sercami97/EstacionMeteorologica/Documentacion/img/ardu.jpg

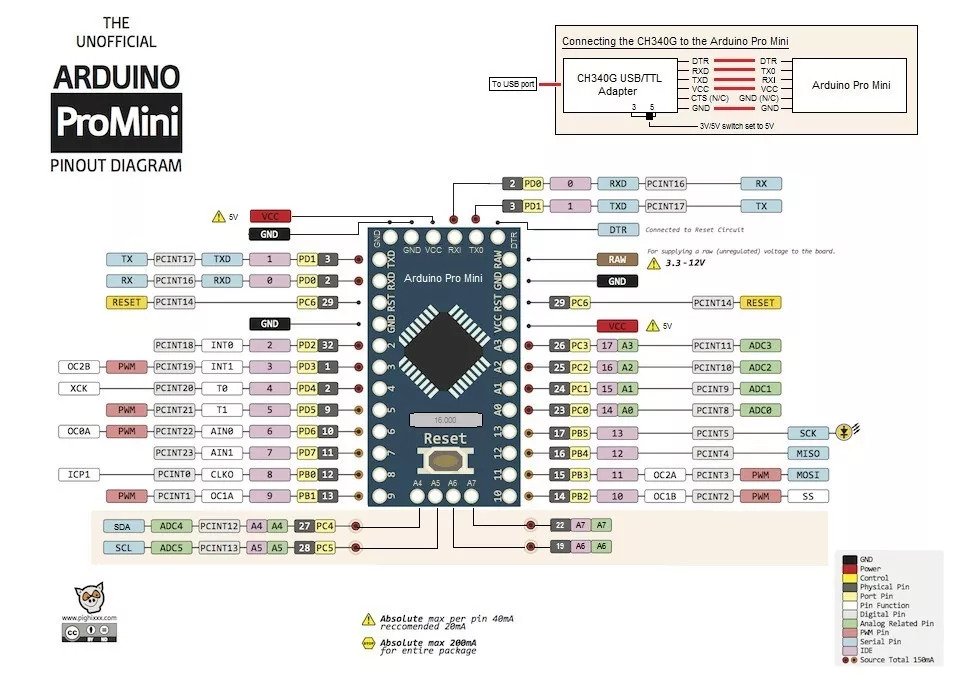
Documentacion/img/ardu.jpg
