sercami97/EstacionMeteorologica/Documentacion/img/dgen.png

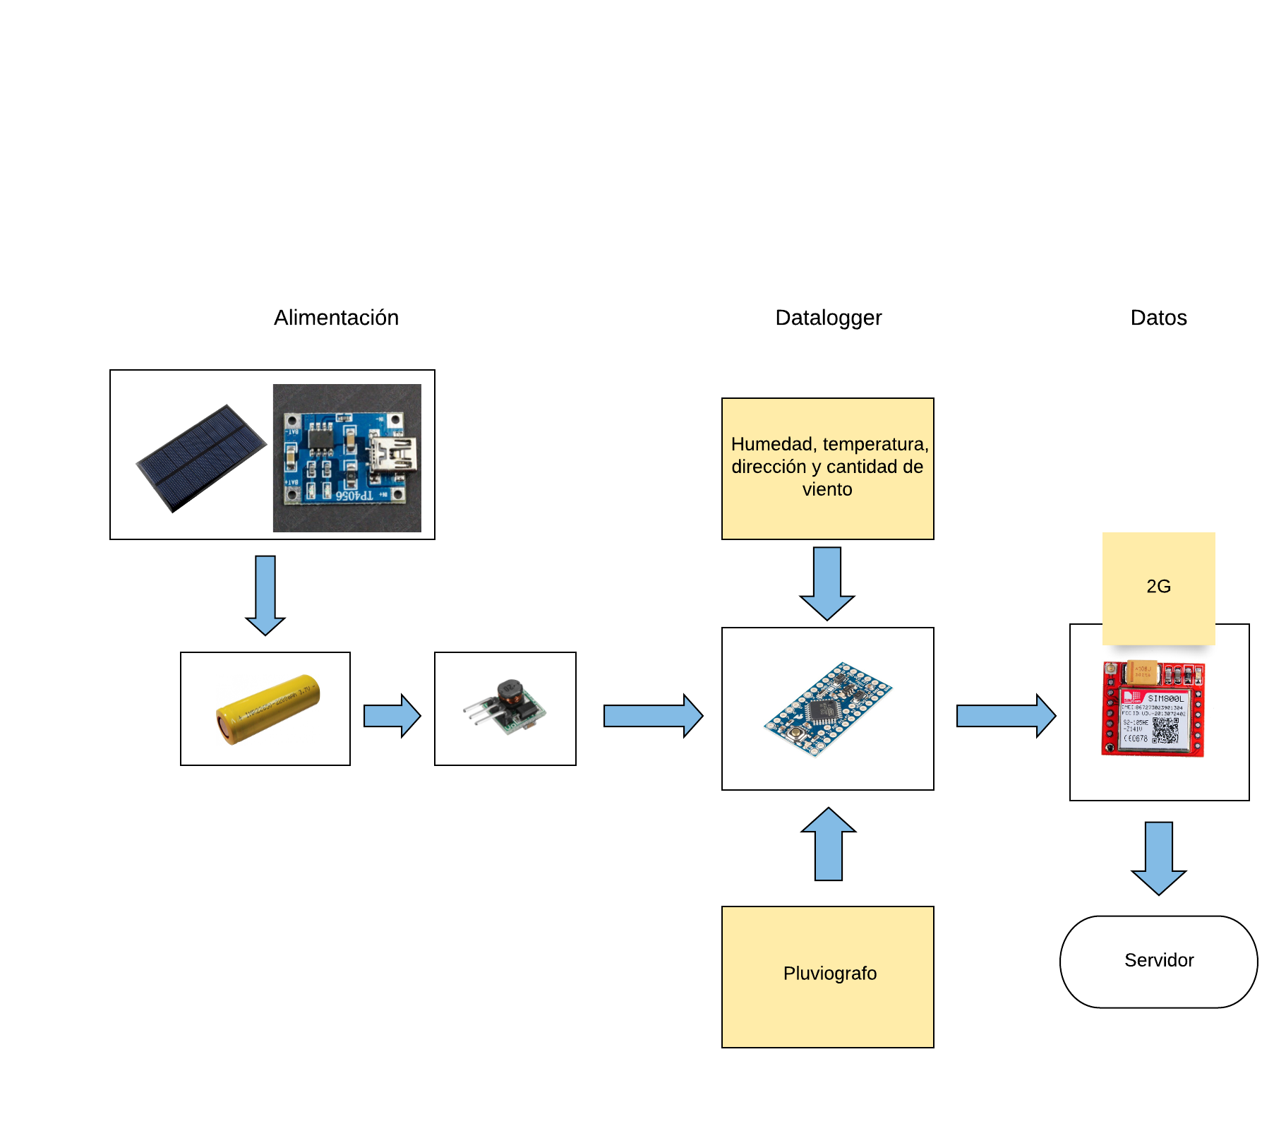
Documentacion/img/dgen.png
