sercami97/EstacionMeteorologica/Documentacion/img/dir_viento.png

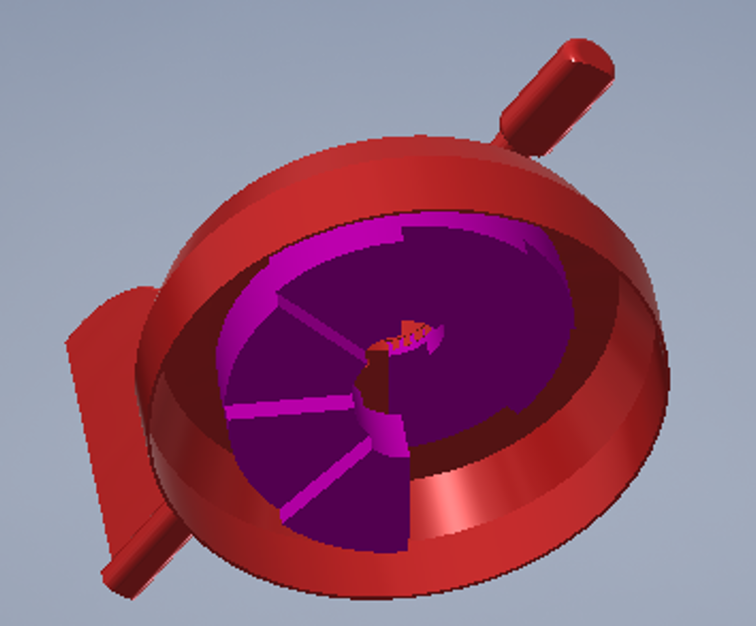
Documentacion/img/dir_viento.png
