sercami97/EstacionMeteorologica/Documentacion/img/dsleep.png

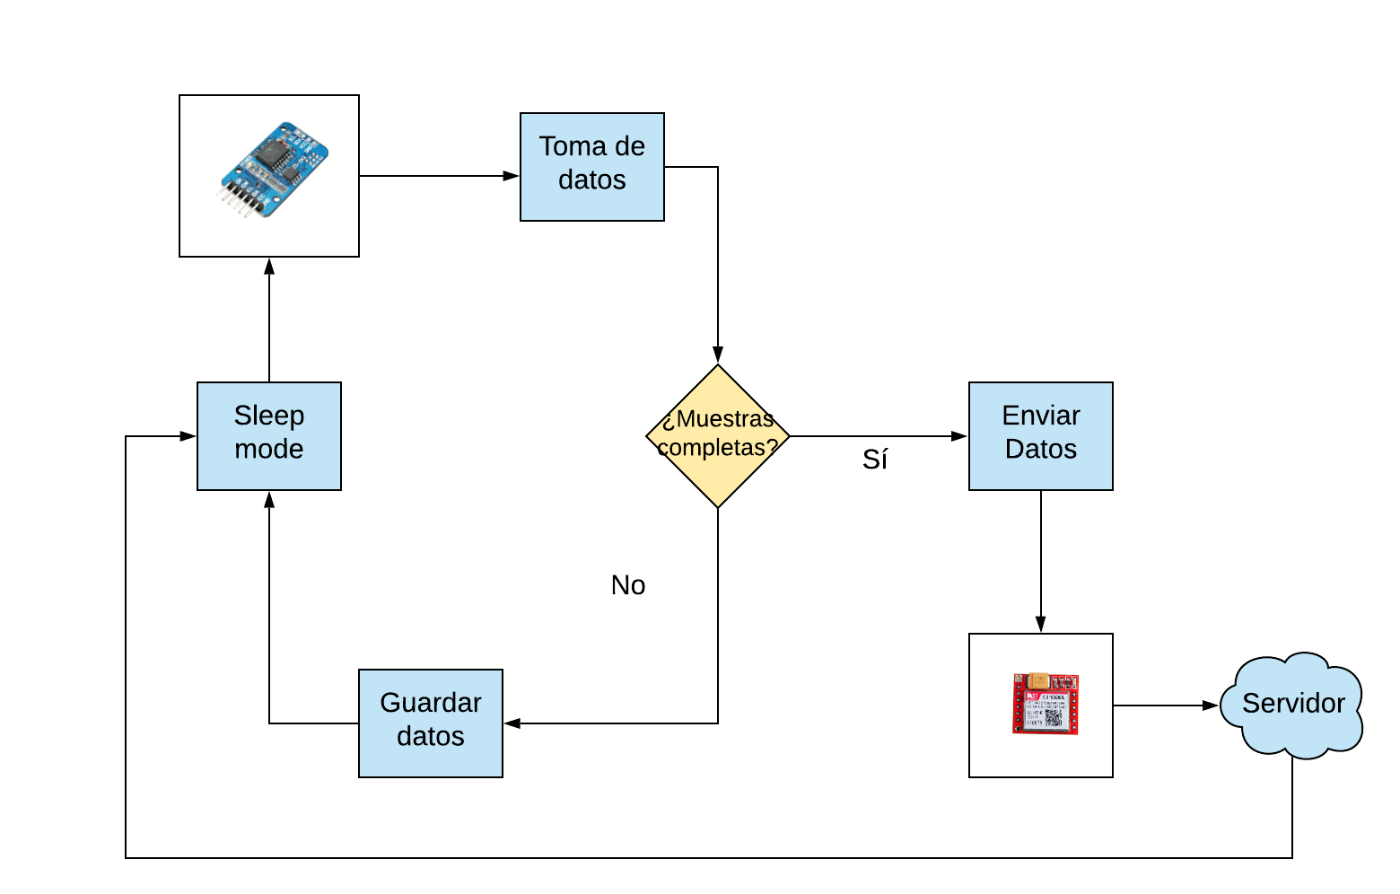
Documentacion/img/dsleep.png
