sercami97/EstacionMeteorologica/Documentacion/img/hall.jpg

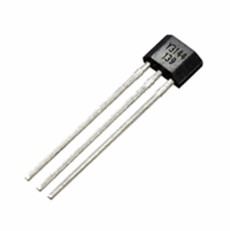
Documentacion/img/hall.jpg
