sercami97/EstacionMeteorologica/Documentacion/img/hall_sheet.png

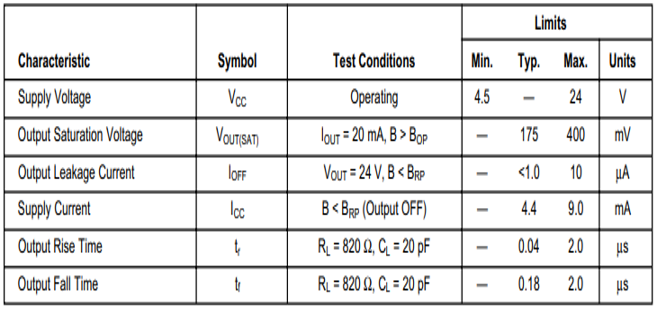
Documentacion/img/hall_sheet.png
