sercami97/EstacionMeteorologica/Documentacion/img/panel.jpg

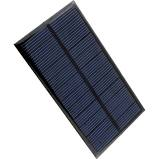
Documentacion/img/panel.jpg
