sercami97/EstacionMeteorologica/Documentacion/img/pcb.PNG

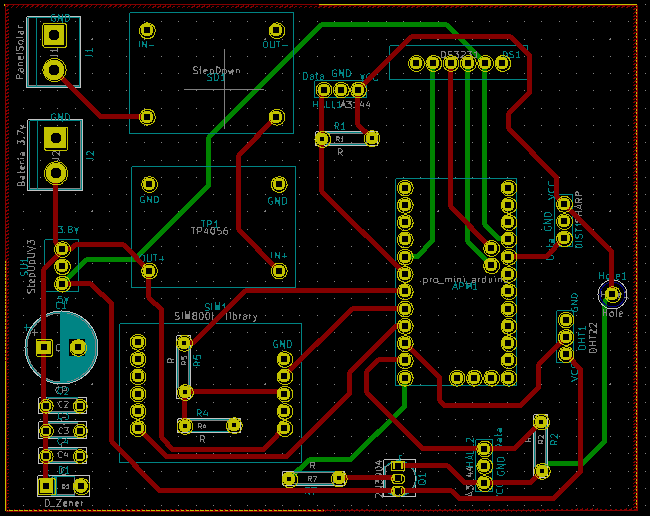
Documentacion/img/pcb.PNG
