sercami97/EstacionMeteorologica/Documentacion/img/pcb_mask.PNG

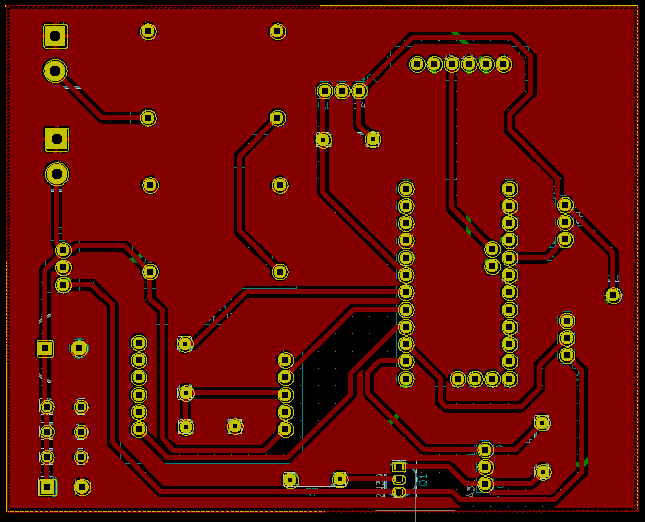
Documentacion/img/pcb_mask.PNG
