sercami97/EstacionMeteorologica/Documentacion/img/pluv.png

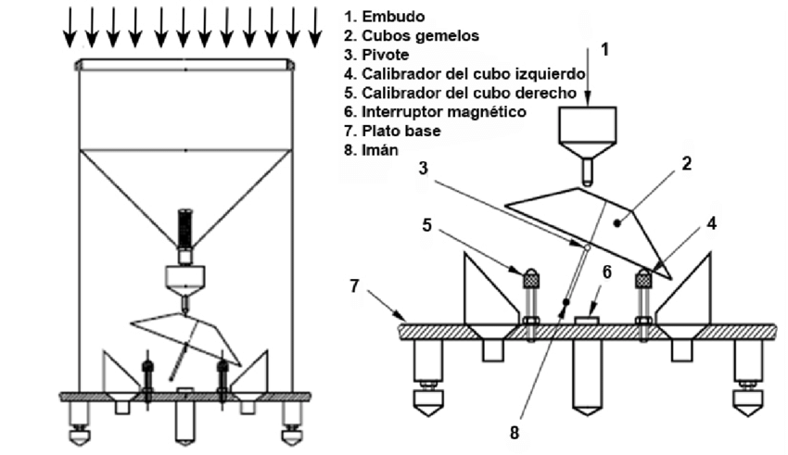
Documentacion/img/pluv.png
