sercami97/EstacionMeteorologica/Documentacion/img/res_final.png

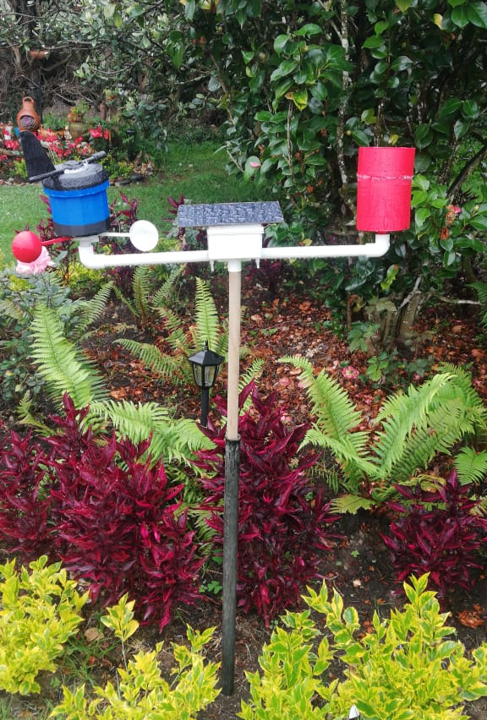
Documentacion/img/res_final.png
