sercami97/EstacionMeteorologica/Documentacion/img/RTC.jpg

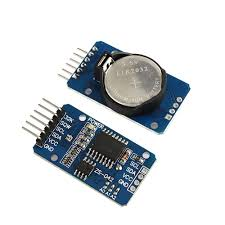
Documentacion/img/RTC.jpg
