sercami97/EstacionMeteorologica/Documentacion/img/sch.PNG

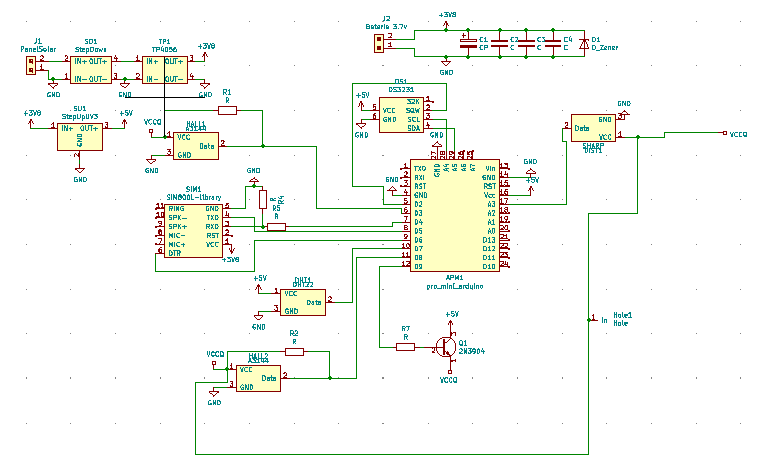
Documentacion/img/sch.PNG
