sercami97/EstacionMeteorologica/Documentacion/img/sim.jpg

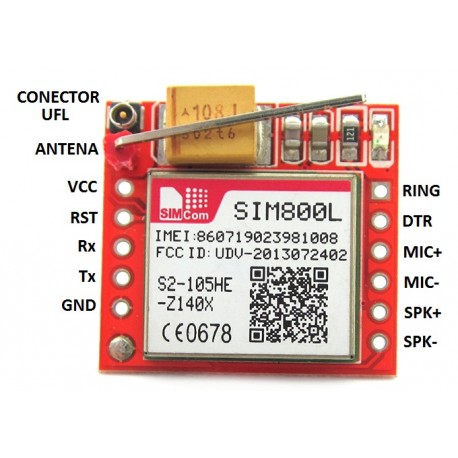
Documentacion/img/sim.jpg
