sercami97/EstacionMeteorologica/Diseños3D/STL_PROTOTIPO/V2/ConexionDireccionBottom.stl

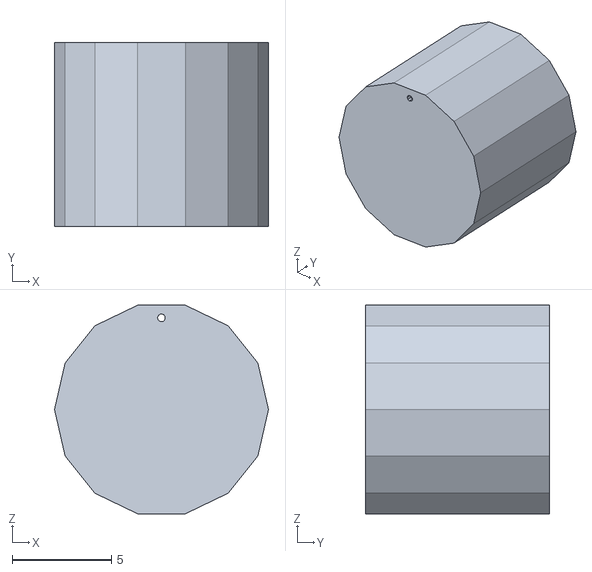
[picture p35: CAD file, 2020-06-29]
Diseños3D/STL_PROTOTIPO/V2/ConexionDireccionBottom.stl
10.8 x 9.30 x 10.5
