sercami97/EstacionMeteorologica/Diseños3D/STL_PROTOTIPO/V2/V/DesnivelSharp2.stl

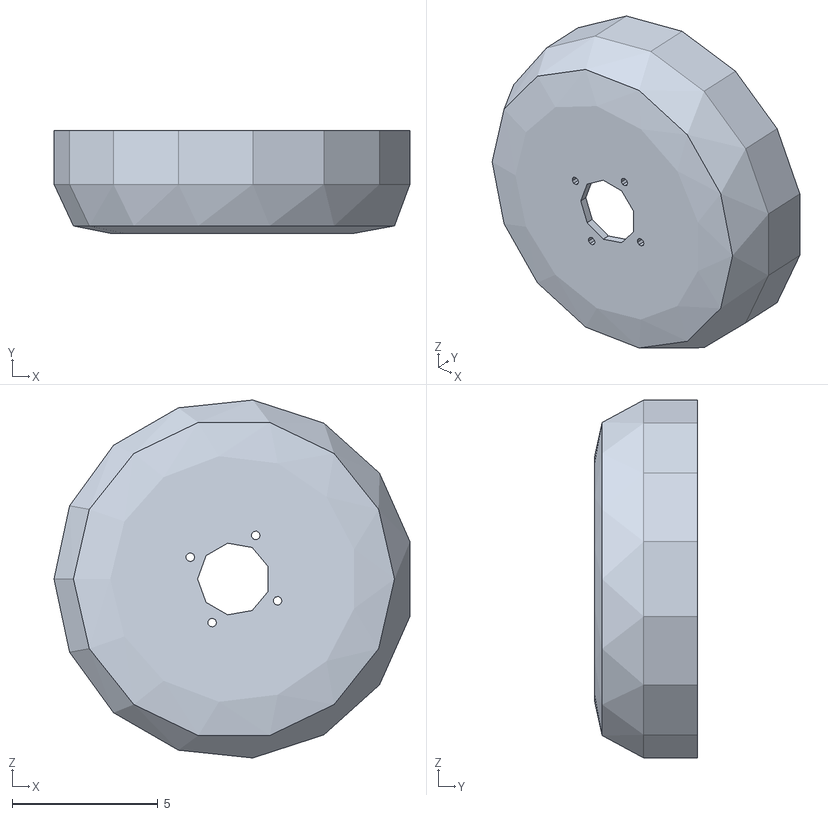
[picture p36: CAD file, 2020-06-29]
Diseños3D/STL_PROTOTIPO/V2/V/DesnivelSharp2.stl
12.2 x 3.53 x 12.3
