sercami97/EstacionMeteorologica/EDITABLES/3D/VersionFinal/STL/7Agosto/Direccion.stl

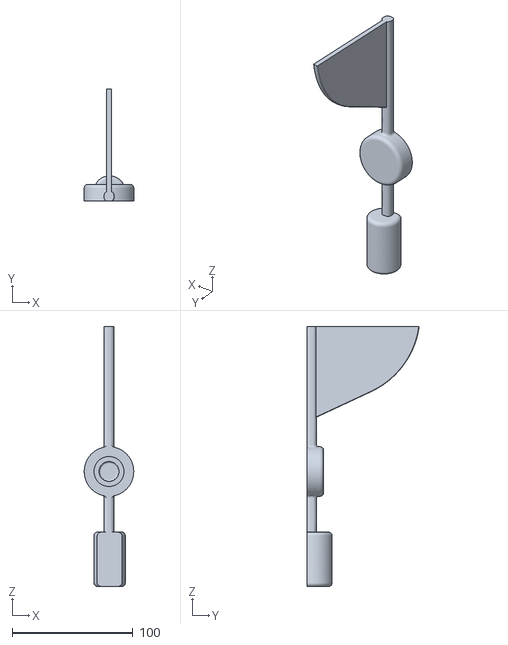
[picture p37: CAD file, 2021-02-24]
EDITABLES/3D/VersionFinal/STL/7Agosto/Direccion.stl
41.0 x 93.0 x 215.0
