sercami97/EstacionMeteorologica/EDITABLES/3D/VersionFinal/STL/8Agosto/CajonInf.stl

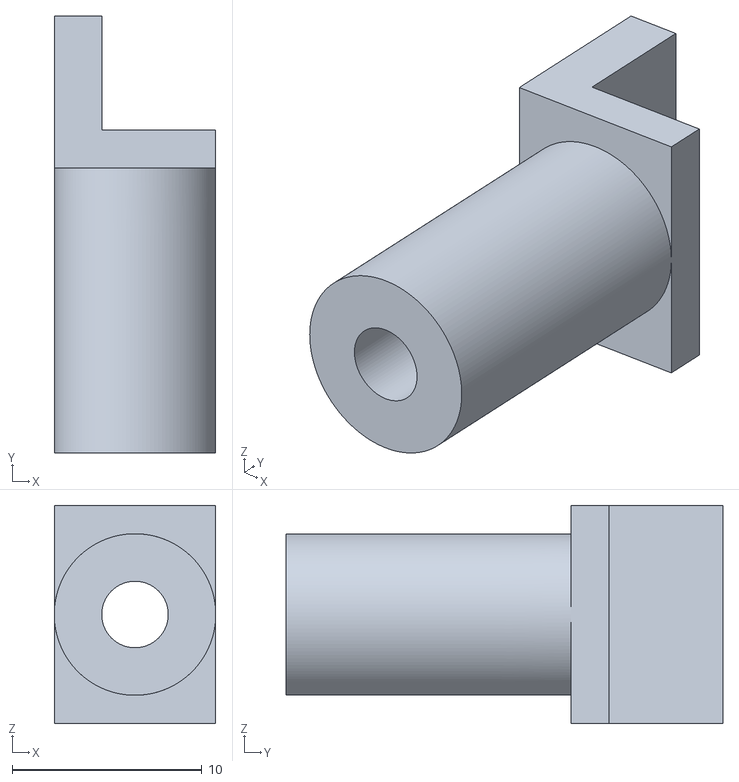
[picture p38: CAD file, 2021-02-24]
EDITABLES/3D/VersionFinal/STL/8Agosto/CajonInf.stl
8.50 x 23.0 x 11.5
