sercami97/EstacionMeteorologica/Diseños3D/STL/VIENTO/9JUN20/DireccionBase.stl

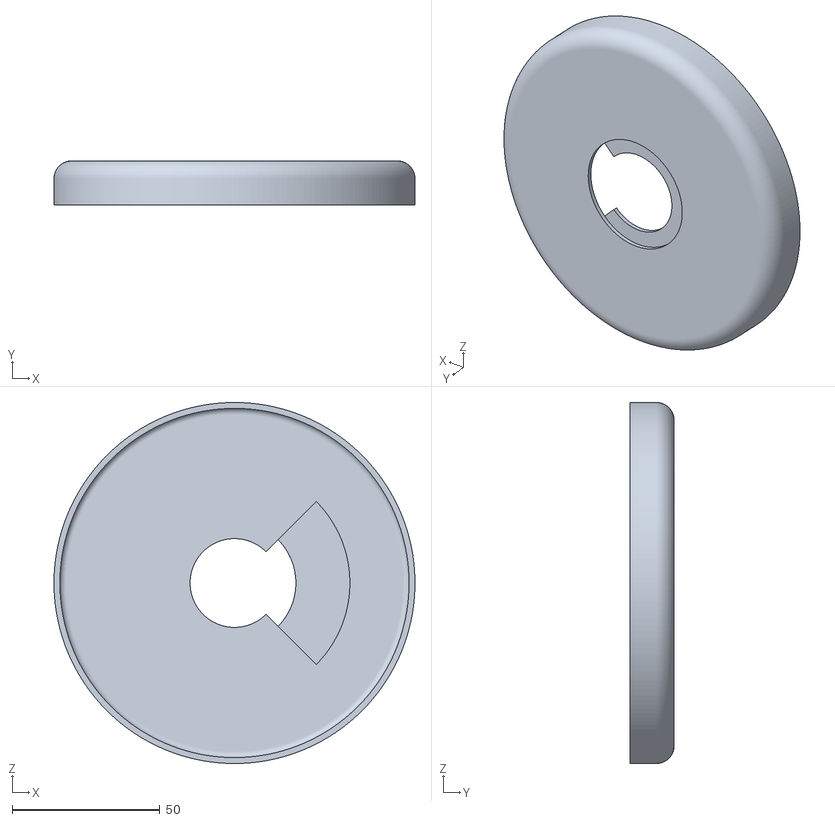
[picture p39: CAD file, 2020-06-29]
Diseños3D/STL/VIENTO/9JUN20/DireccionBase.stl
122.0 x 15.0 x 122.0
