sercami97/EstacionMeteorologica/Diseños3D/STL/VIENTO/PlatoHumedadDireccion.stl

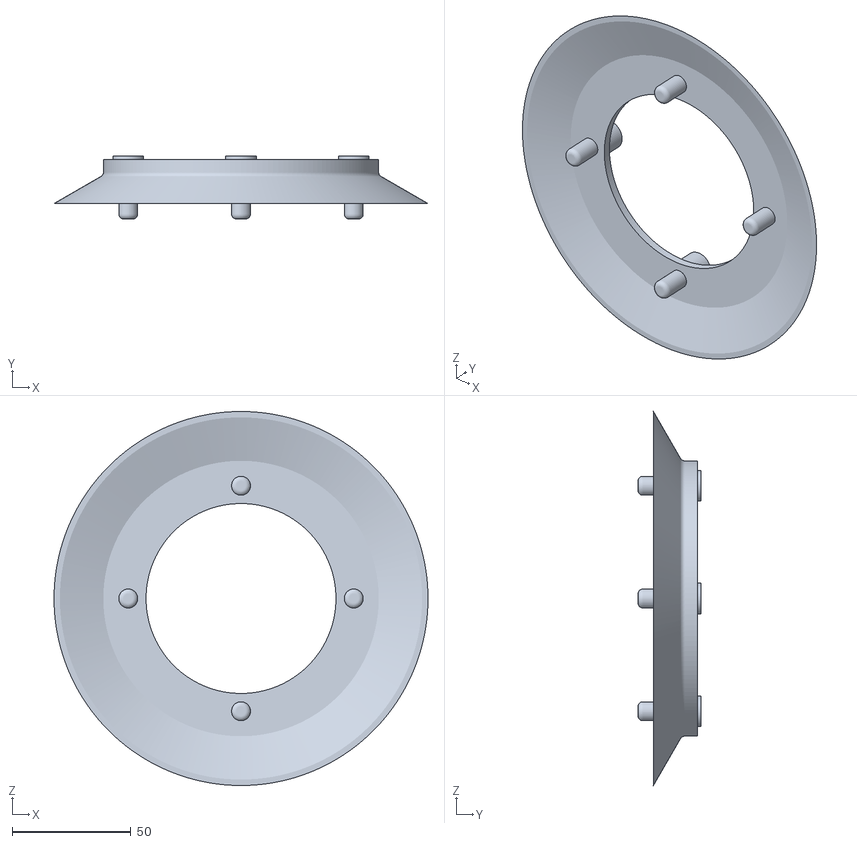
[picture p40: CAD file, 2020-04-06]
Diseños3D/STL/VIENTO/PlatoHumedadDireccion.stl
157.6 x 26.5 x 157.6
