sercami97/EstacionMeteorologica/Diseños3D/STL_PROTOTIPO/Febrero27/spherewind.stl

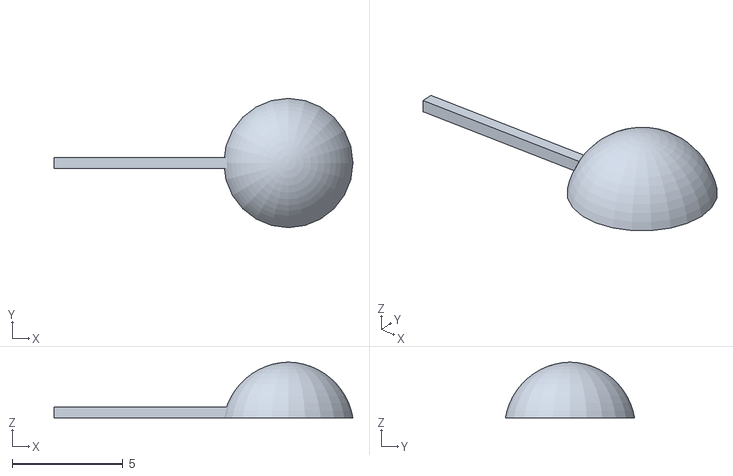
[picture p41: CAD file, 2020-06-29]
Diseños3D/STL_PROTOTIPO/Febrero27/spherewind.stl
13.5 x 5.83 x 2.52
