sercami97/EstacionMeteorologica/Diseños3D/STL_PROTOTIPO/V2/Direccion.stl

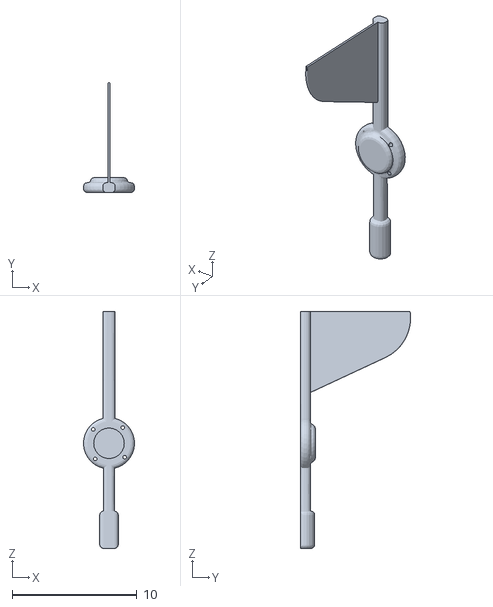
[picture p42: CAD file, 2020-06-29]
Diseños3D/STL_PROTOTIPO/V2/Direccion.stl
4.10 x 8.84 x 19.0
