sercami97/EstacionMeteorologica/EDITABLES/3D/VersionFinal/STL/7Agosto/BasePlu.stl

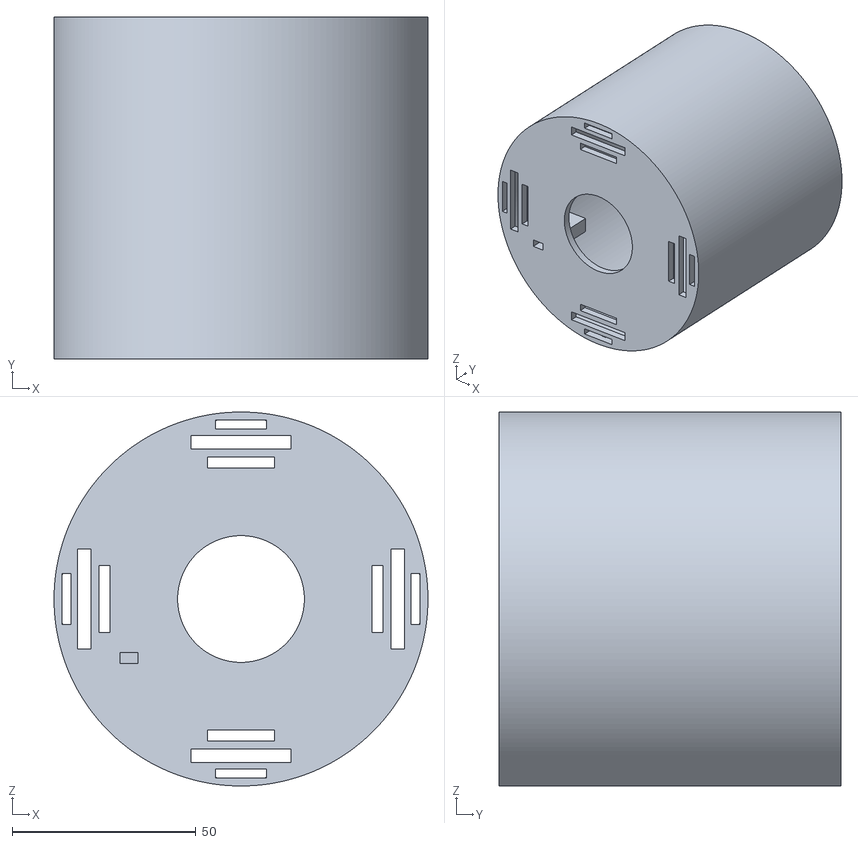
[picture p43: CAD file, 2021-02-24]
EDITABLES/3D/VersionFinal/STL/7Agosto/BasePlu.stl
101.8 x 93.0 x 101.8
