sercami97/EstacionMeteorologica/EDITABLES/3D/VersionFinal/STL/8Agosto/SujetorPanel.stl

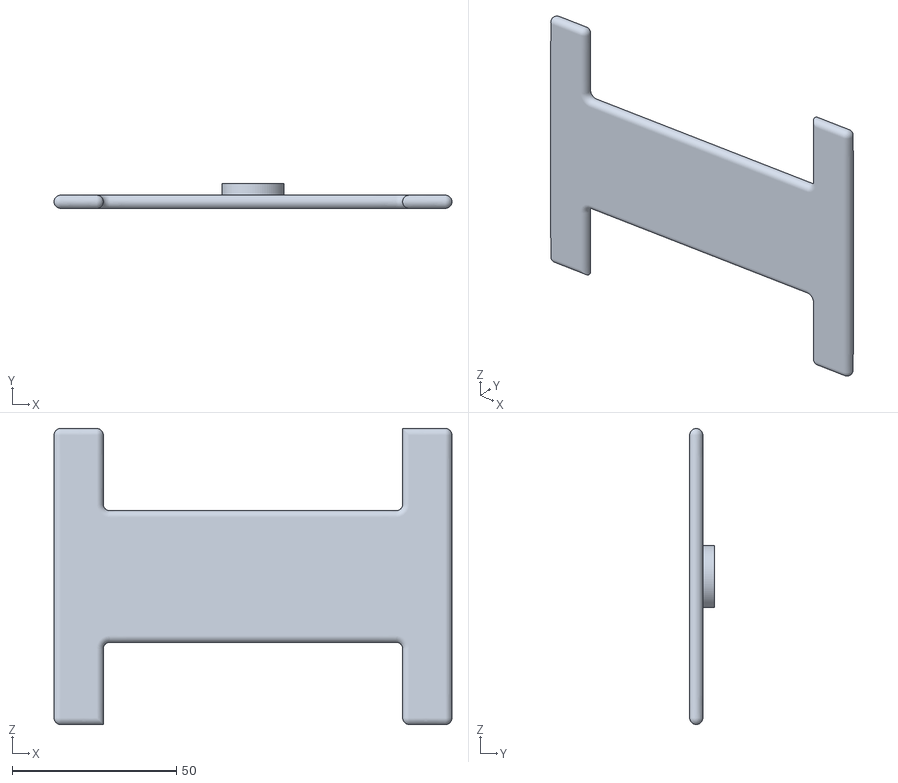
[picture p44: CAD file, 2021-02-24]
EDITABLES/3D/VersionFinal/STL/8Agosto/SujetorPanel.stl
121.0 x 7.50 x 90.0
