sercami97/EstacionMeteorologica/Diseños3D/STL/VIENTO/9JUN20/DireccionEscalones.stl

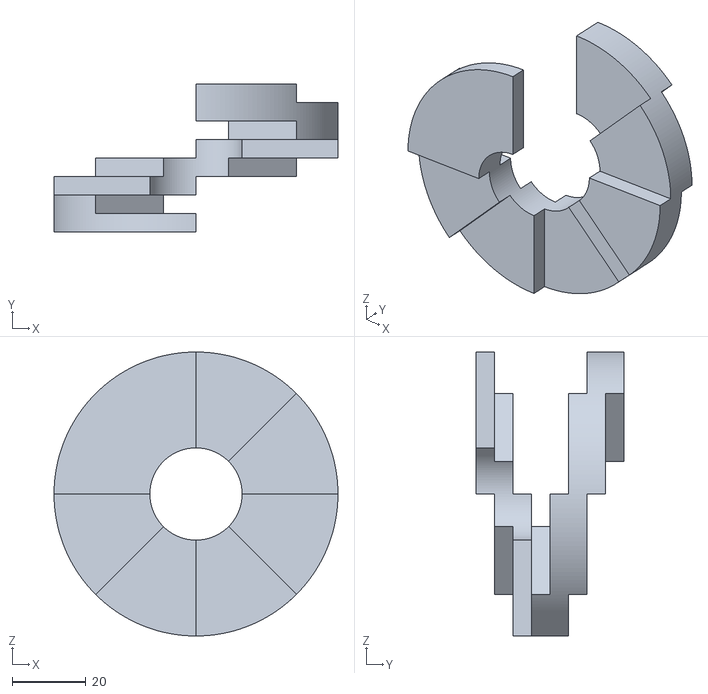
[picture p45: CAD file, 2020-06-29]
Diseños3D/STL/VIENTO/9JUN20/DireccionEscalones.stl
77.0 x 40.0 x 77.0
