sercami97/EstacionMeteorologica/Diseños3D/STL_PROTOTIPO/Febrero27/CajonReed.stl

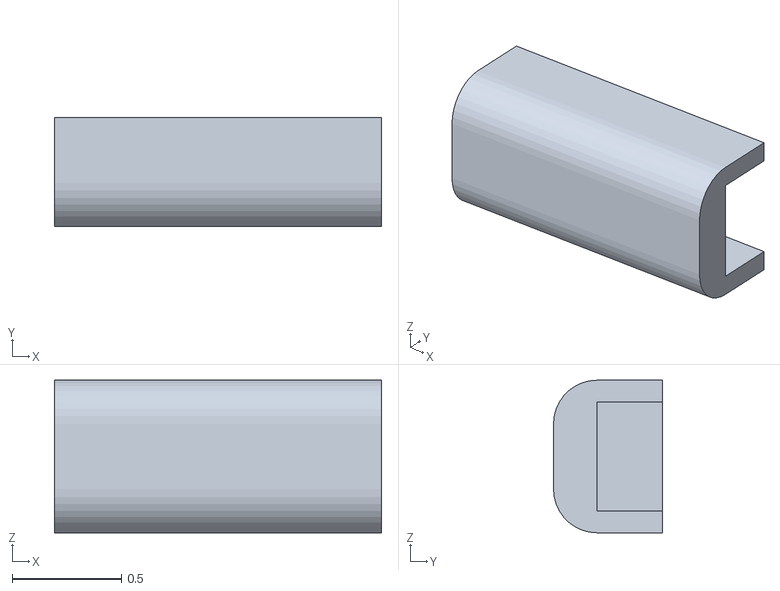
[picture p46: CAD file, 2020-06-29]
Diseños3D/STL_PROTOTIPO/Febrero27/CajonReed.stl
1.50 x 0.5 x 0.7
