sercami97/EstacionMeteorologica/Diseños3D/STL_PROTOTIPO/Test/Base Anemometro.stl

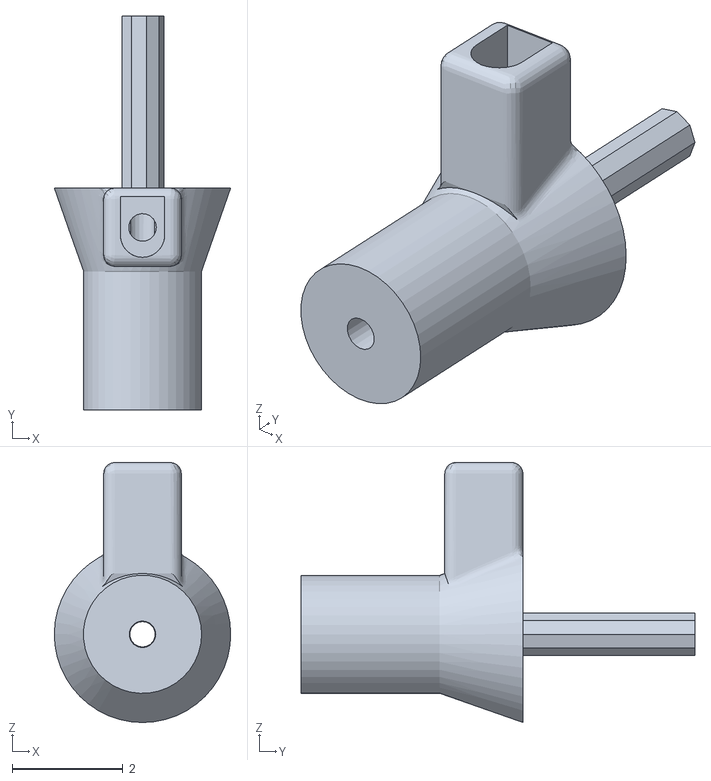
[picture p47: CAD file, 2020-06-29]
Diseños3D/STL_PROTOTIPO/Test/Base Anemometro.stl
3.18 x 7.10 x 4.69
