sercami97/EstacionMeteorologica/EDITABLES/3D/VersionFinal/STL/7Agosto/BaseComplePlu.stl

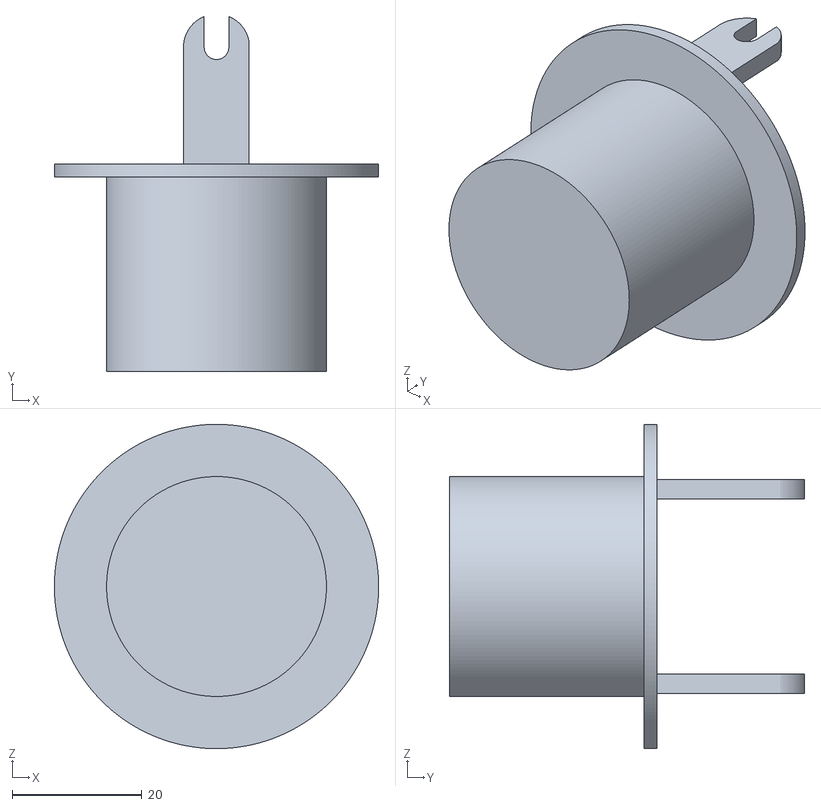
[picture p48: CAD file, 2021-02-24]
EDITABLES/3D/VersionFinal/STL/7Agosto/BaseComplePlu.stl
50.0 x 54.7 x 50.0
