sercami97/EstacionMeteorologica/EDITABLES/3D/VersionFinal/STL/8Agosto/BasePaletasBottom.stl

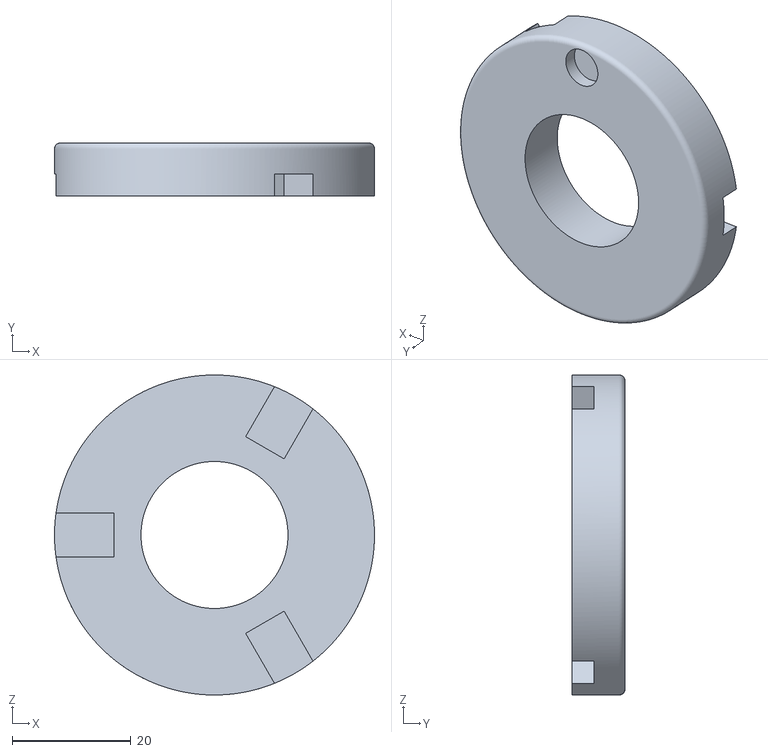
[picture p49: CAD file, 2021-02-24]
EDITABLES/3D/VersionFinal/STL/8Agosto/BasePaletasBottom.stl
54.0 x 9.00 x 54.0
