sercami97/EstacionMeteorologica/Diseños3D/STL/VIENTO/9JUN20/PruebaRodamiento.stl

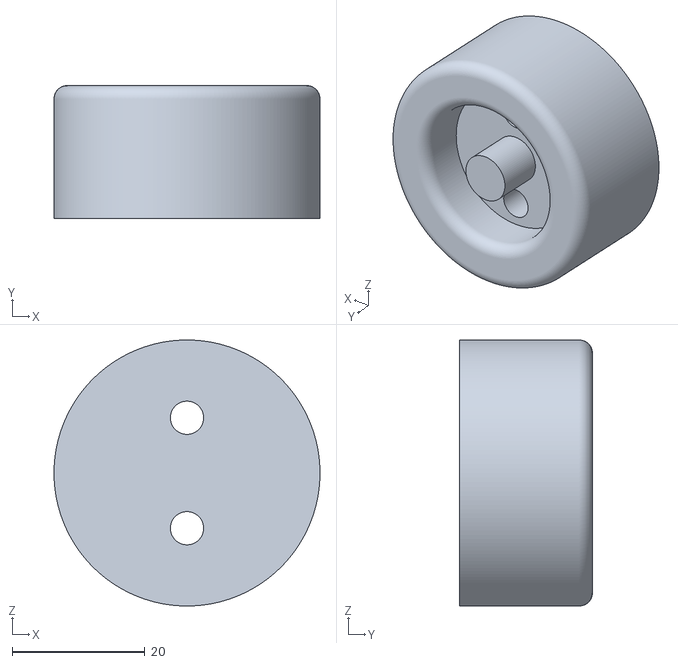
[picture p50: CAD file, 2020-06-29]
Diseños3D/STL/VIENTO/9JUN20/PruebaRodamiento.stl
40.0 x 20.0 x 40.0
