sercami97/EstacionMeteorologica/Diseños3D/STL_PROTOTIPO/Febrero27/BasePaletas.stl

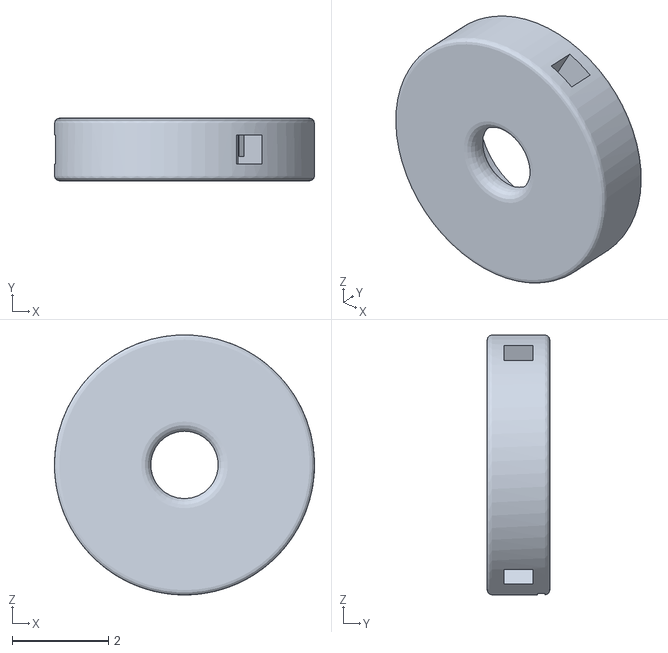
[picture p51: CAD file, 2020-06-29]
Diseños3D/STL_PROTOTIPO/Febrero27/BasePaletas.stl
5.40 x 1.30 x 5.40
