sercami97/EstacionMeteorologica/Diseños3D/STL_PROTOTIPO/Test/ConexionDireccionTop.stl

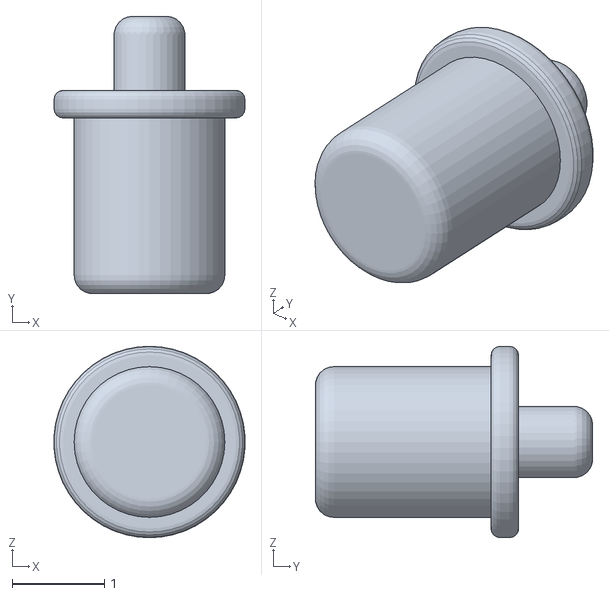
[picture p52: CAD file, 2020-06-29]
Diseños3D/STL_PROTOTIPO/Test/ConexionDireccionTop.stl
2.07 x 3.00 x 2.07
