sercami97/EstacionMeteorologica/EDITABLES/3D/VersionFinal/STL/8Agosto/BasePaletasTop.stl

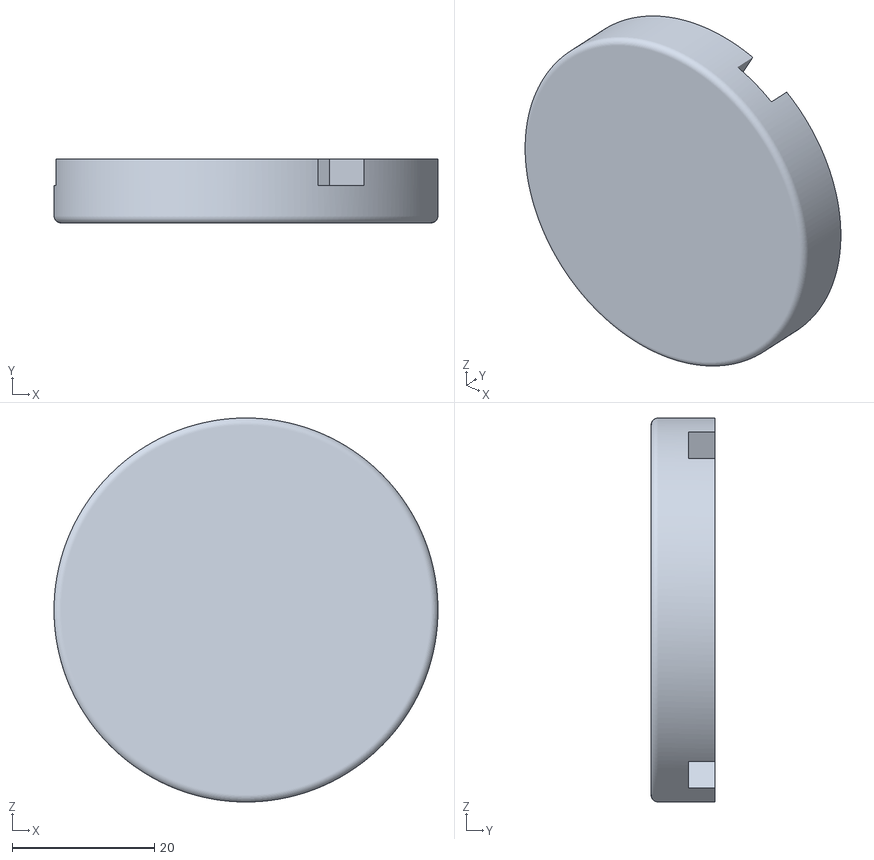
[picture p53: CAD file, 2021-02-24]
EDITABLES/3D/VersionFinal/STL/8Agosto/BasePaletasTop.stl
54.0 x 9.00 x 54.0
