sercami97/EstacionMeteorologica/Diseños3D/STL/VIENTO/9JUN20/SoportePulgadaMitad.stl

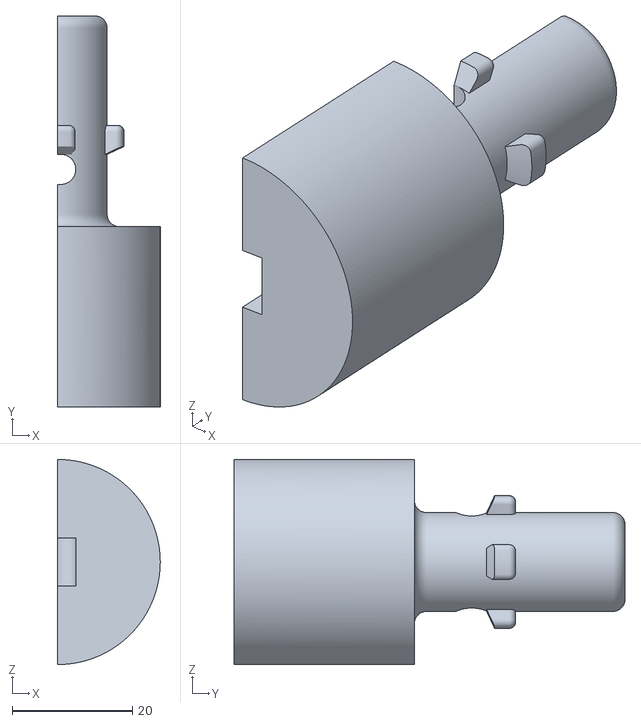
[picture p54: CAD file, 2020-06-29]
Diseños3D/STL/VIENTO/9JUN20/SoportePulgadaMitad.stl
17.0 x 65.0 x 34.1
