sercami97/EstacionMeteorologica/EDITABLES/3D/VersionFinal/STL/8Agosto/Caja_Inferior.stl

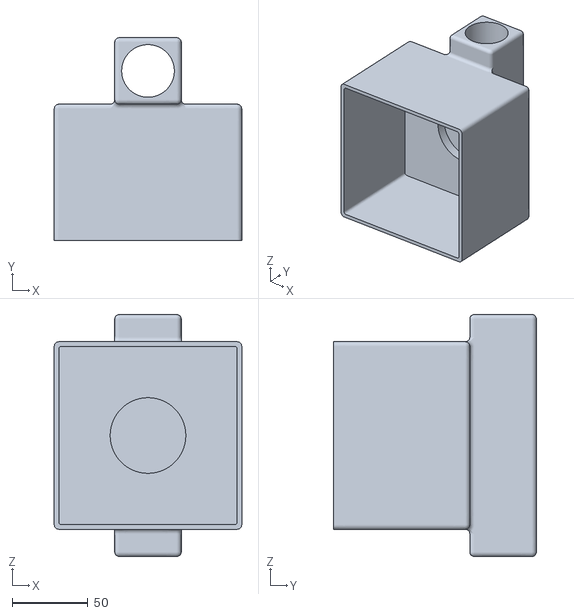
[picture p55: CAD file, 2021-02-24]
EDITABLES/3D/VersionFinal/STL/8Agosto/Caja_Inferior.stl
124.0 x 134.0 x 160.0
