sercami97/EstacionMeteorologica/EDITABLES/3D/VersionFinal/STL/8Agosto/CajonSup.stl

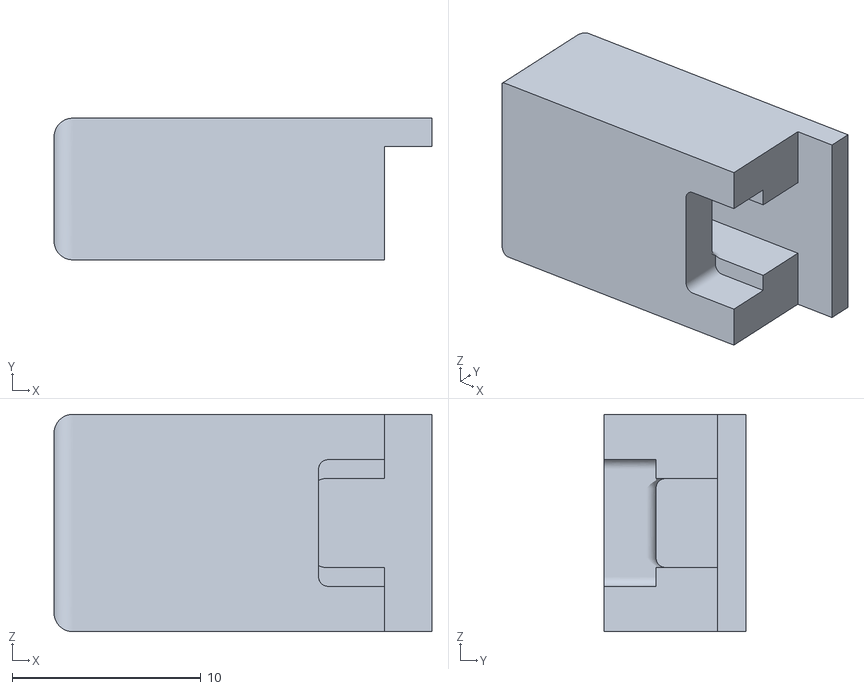
[picture p56: CAD file, 2021-02-24]
EDITABLES/3D/VersionFinal/STL/8Agosto/CajonSup.stl
20.0 x 7.50 x 11.5
