sercami97/EstacionMeteorologica/CodigoArduino/Datalogger_Final/Datalogger_Final.ino

#include "Arduino.h"
#include <Wire.h>
#include <SoftwareSerial.h>
#include "DHT.h" // Libreria DHT de Adafruit para DHT 11 o DHT 22 https://github.com/adafruit/DHT-sensor-library/archive/master.zip
#include <avr/sleep.h> //Libreria avr que contiene los metodos que controlan el modo sleep
#include <DS3232RTC.h>  //Libreria RTC https://github.com/JChristensen/DS3232RTC

//DHT
#define DHTPIN 7     //Pin donde está conectado el sensor DHT
#define DHTTYPE DHT22   //Sensor DHT22
DHT dht(DHTPIN, DHTTYPE);
float h;  //Variable de humedad relativa (0-100)
float temp; //Variable temeperatura grados centigrados

//HALL
#define  hall_an 3  //Pin Anemometro (Vel. Viento)
#define  hall_pluv1 8 //Pin Anemometro (Pluviografo1)
int hallCounter = 0;   //Contador tic tocs anemometro
int hallState = 0;         //Estado actual del sensor efecto hall anemometro (HIGH,LOW)
int lastHallState = 0;     //Estado previo del sensor efecto hall anemometro (HIGH,LOW)
int hallCounter1 = 0;   //Contador tic tocs ´pluviografo
int hallState1 = 0;      //Estado actual del sensor efecto hall pluviografo (HIGH,LOW)
int lastHallState1 = 0;    //Estado previo del sensor efecto hall pluviografo (HIGH,LOW)

//Variables 
//Variables de tiempo para el sensado del anemometro y el pluviografo
float starttime;
float new_endtime = 0;
int len;

//Numero de tomas y Sleep Mode
#define transistor_Pin 9   //Pin del transistor
#define interruptPin 2 //Pin de interrupcion para despertar el arduino
const int time_interval = 30; //Intervalo de tiempo para la toma de datos
int ciclo = 0; 
const int num_ciclos = 5; //Definir numero de tomas previas al envío (tomar 9 como valor máximo para evitar problemas de inestabilidad)
int wake_up_min; //Variable de tiempo en el que se despierta el arduino
bool date_done = false;

//SIM
SoftwareSerial mySerial(5, 4);//TX,RX

// Infrarojo
int WV;
int direccion; //Variable de direccion como entero, tomara valores (1-9)

//Outputs
//Strings en donde se almacenan los datos tomados
String finalString;
String msg;

void setup() {
  delay(5000);
  Serial.begin(9600);
  inicializar(); //Inicializar pines sensores efecto hall y dht
  msg.reserve(290); //Reservar memoria en bytes para la cadena de caracteres de los datos
  mySerial.begin(9600);
  delay(1000);
  
  //Inicializar el modulo SIM800L en bajo consumo energetico
  mySerial.println("AT\r");
  runSerial();
  delay(1000);
  mySerial.println("AT+CSCLK=2\r");
  runSerial();
  delay(1000);

  //Inicializar Sleep Mode
  inicializarSM(); 
}

void inicializar() {
  //Declarar pines de la señal de los sensores efecto hall como inputs
  pinMode(hall_an, INPUT); 
  pinMode(hall_pluv1, INPUT);
  //Inicializar el DHT
  dht.begin();
}

void inicializarSM() {
  //Declarar pines necesarios para el funcionamiento del sleep mode
  pinMode(interruptPin, INPUT_PULLUP);
  pinMode(transistor_Pin, OUTPUT);
  pinMode(transistor_Pin, HIGH);

  //Eliminar cualquier alarma previa
  RTC.setAlarm(ALM1_MATCH_DATE, 0, 0, 0, 1);
  RTC.setAlarm(ALM2_MATCH_DATE, 0, 0, 0, 1);
  RTC.alarm(ALARM_1);
  RTC.alarm(ALARM_2);
  RTC.alarmInterrupt(ALARM_1, false);
  RTC.alarmInterrupt(ALARM_2, false);
  RTC.squareWave(SQWAVE_NONE);   

  //Configuración de la fecha
  if (date_done == false){
  tmElements_t tm;
  tm.Hour = 13;
  tm.Minute = 22;
  tm.Second = 00;
  tm.Day = 5;
  tm.Month = 8;
  tm.Year = 2020 - 1970;
  RTC.write(tm);   
  }

  date_done = true;
  
  time_t  t = RTC.get(); //Obtener el tiempo actual del RTC
  wake_up_min = minute(t) + time_interval;
  
  //Condicional necesario para cambio de horas
  if (wake_up_min >= 60){
    wake_up_min = wake_up_min - 60;
  }
  
  RTC.setAlarm(ALM1_MATCH_MINUTES , 0, wake_up_min, 0, 0); //Poner alarma
  RTC.alarm(ALARM_1); //Eliminar bandera de la alarma
  RTC.squareWave(SQWAVE_NONE);
  RTC.alarmInterrupt(ALARM_1, true);  //Habilitar interrupcion de "ALARM_1"
}

void initModule(){
  //Comandos AT necesarios para GSM/GPRS 
  mySerial.println(F("AT+SAPBR=3,1,\"Contype\",\"GPRS\""));
  runSerial();
  delay(1500);
  mySerial.println(F("AT+SAPBR=3,1,\"APN\",\"internet.comcel.com.co\""));
  runSerial();
  delay(100);
  mySerial.println(F("AT+SAPBR=3,1,USER,\"comcel\""));
  runSerial();
  delay(100);
  mySerial.println(F("AT+SAPBR=3,1,PWD,\"comcel\""));
  runSerial();
  delay(100);
  mySerial.println(F("AT+SAPBR=1,1"));
  runSerial();
  delay(3500);
  mySerial.println(F("AT+SAPBR=2,1"));
  runSerial();
  delay(2500);
}

void loop() {
  //Loop principal, se realizan n = "num_ciclos" toma de datos antes de hacer 
  //post en el servidor y borrar los datos del intervalo de tiempo en cuestion
  while (ciclo < num_ciclos){
    Going_To_Sleep();
  }
  
  delay(10000); 
  mySerial.println("AT\r");
  runSerial();
  delay(1000);
  mySerial.println("AT+CSCLK=0\r"); //Comando AT usado para establecer el modulo SIM800L en funcionamiento normal  
  runSerial();
  delay(1000);
  messageServerGet(); //Envío del mensaje en el servidor
  msg.remove(0,290); //Se elimina el mensaje enviado
  msg.reserve(290); //Se vuelve a disponer 290bytes de memoria para el nuevo mensaje
  //Comandos AT necesarios para ordenar al SIM800L entrar en sleep mode
  mySerial.println("AT\r");
  runSerial();
  delay(1000);
  mySerial.println("AT+CSCLK=2\r");
  runSerial();
  delay(1000);
  ciclo = 0;
  inicializarSM();
}

void Going_To_Sleep() {
    digitalWrite(transistor_Pin, LOW);
    sleep_enable();//Habilitar sleep mode
    attachInterrupt(0, wakeUp, LOW); //Adjuntar la interrupcion al pin D2
    set_sleep_mode(SLEEP_MODE_PWR_DOWN);//Modo full sleep
    delay(1000); 
    sleep_cpu();//Activar sleep mode
    digitalWrite(transistor_Pin, HIGH); //Habilitar nodo 5V de alimentacion sensores
    delay(5000);
    tomaDatos(); //Tomar datos de las variables de interes
    time_t t = RTC.get();
    wake_up_min = minute(t) + time_interval;
    if (wake_up_min >= 60){
      wake_up_min =  wake_up_min - 60;
    }
    RTC.setAlarm(ALM1_MATCH_MINUTES , 0, wake_up_min, 0, 0); //Poner nueva alarma
    RTC.alarm(ALARM_1);
    ciclo ++; //Sumar un ciclo de sensado
}

void wakeUp() {
  Serial.println(F("Interrrupt Fired"));
  sleep_disable();//Deshabilitar sleep mode
  detachInterrupt(0); //Eliminar la interrupcion del pin 2;
}

void tomaDatos() {
  hallCounter = 0;
  hallCounter1 = 0;
  hall(); //Ejecutar funcion para el sensado con los efecto hall (pluviografo y anemometro)
  temp_hum(); //Ejecutar funcion para el sensado de temperatura y humedad
  dir(); //Ejecutar funcion para el sensado de la direccion
  time_t tiempo = RTC.get(); 
  //Guardar datos en un String
  finalString = String(day(tiempo))+ "," + String(month(tiempo))+ "," + String(hour(tiempo))+ "," + String(minute(tiempo)) + "," + String(int(temp)) + "," + String(int(h)) + "," + String(hallCounter) + "," + String(direccion) + "," + String(hallCounter1)+ ";";
  msg = msg + finalString; //Guardar la toma de diferentes ciclos en una variable que sera enviada al servidor
  Serial.println(msg);
}

void hall() {
  starttime = millis();
  Serial.println(starttime);
  while ((new_endtime - starttime) < 45000) { //Realizar este loop durante 45 segundos
    hallState = digitalRead(hall_an); //Estado hall anemometro
    hallState1 = digitalRead(hall_pluv1); //Estado hall pluviografo 1
    
    //Si hay un cambio en el estado HIGH ->LOW o LOW->HIGH en la señal de salida de los efecto hall
    //se aumenta en 1 el numero de tic tocs
    if (hallState != lastHallState) { 
      if (hallState == HIGH) {
        hallCounter ++;
      }
      delay(50);
    }
    if (hallState1 != lastHallState1) {
      if (hallState1 == HIGH) {
        hallCounter1 ++;
      }
      delay(50);
    }
    lastHallState = hallState;
    lastHallState1 = hallState1;
    new_endtime = millis();
  }
}

void temp_hum() {
  h = dht.readHumidity(); //Leer la humedad relativa
  temp = 10*dht.readTemperature(); //Leer temperatura en grados Celsius
}

void dir(){

  //Dependiendo del valor analogo obtenido de la señal del sensor infrarrojo se establece la direccion
  //Curva característica usada: d = 33.9 + -69.5v + 62.3v^2 + -25.4v^3 + 3.83v^4

    WV = analogRead(A3);

    if ( WV >= 286 && WV < 328){
      direccion = 1; // Norte
    }
    else if (WV >= 246 && WV < 286){
      direccion = 2; //NOR
    }
    else if (WV >= 220 && WV < 246){
      direccion = 3; //OR
    }
    else if (WV >= 200 && WV < 220){
      direccion = 4; //SOR
    }
    else if (WV >= 184 && WV < 200){
      direccion = 5; //S
    }  
    else if (WV >= 173 && WV < 184){
      direccion = 6; //SOC
    }
    else if (WV >= 164 && WV < 173){
      direccion = 7; //OC
    }
    else if (WV >= 153 && WV < 164){
      direccion = 8; //NOC
    }
    else{
      direccion = 9; //NA
    }
}

void messageServerGet(){

   len = msg.length();
   msg.remove(len-1);
   Serial.println(msg);
   delay(2000);
   initModule(); //Inicializacion del modulo
   //Comandos AT necesarios para postear el mensaje final en el servidor
   delay(5000);
   mySerial.println(F("AT+HTTPINIT\r")); //Initializes the HTTP service. This is a proprietary Simcom AT command.This command should be sent first before starting HTTP service.
   runSerial();
   delay(500);
   mySerial.println(F("AT+HTTPPARA=\"CID\",1\r"));//sets up HTTP parameters for the HTTP call. This is a proprietary AT command from SIMCOM.
   runSerial();
   delay(500);
   mySerial.println("AT+HTTPPARA=\"URL\",\"http://eco.agromakers.org/api/v1/sensor/reporte_varios?id=2020080427&tramo="+msg+"\"\r");
   runSerial();
   delay(500);
   mySerial.println(F("AT+HTTPACTION=0\r"));
   runSerial();
   delay(3000);
   mySerial.println(F("AT+HTTPREAD=0,100\r"));
   runSerial();
   delay(500);
   mySerial.println(F("AT+HTTPTERM\r"));
   runSerial();
   delay(3000);
}

void runSerial(){
    while (mySerial.available()){
      Serial.write(mySerial.read());  
    }
}
